danielhokanson/3input-3output-LiFePO4-BatteryBank/sim/output/thermal_year.png

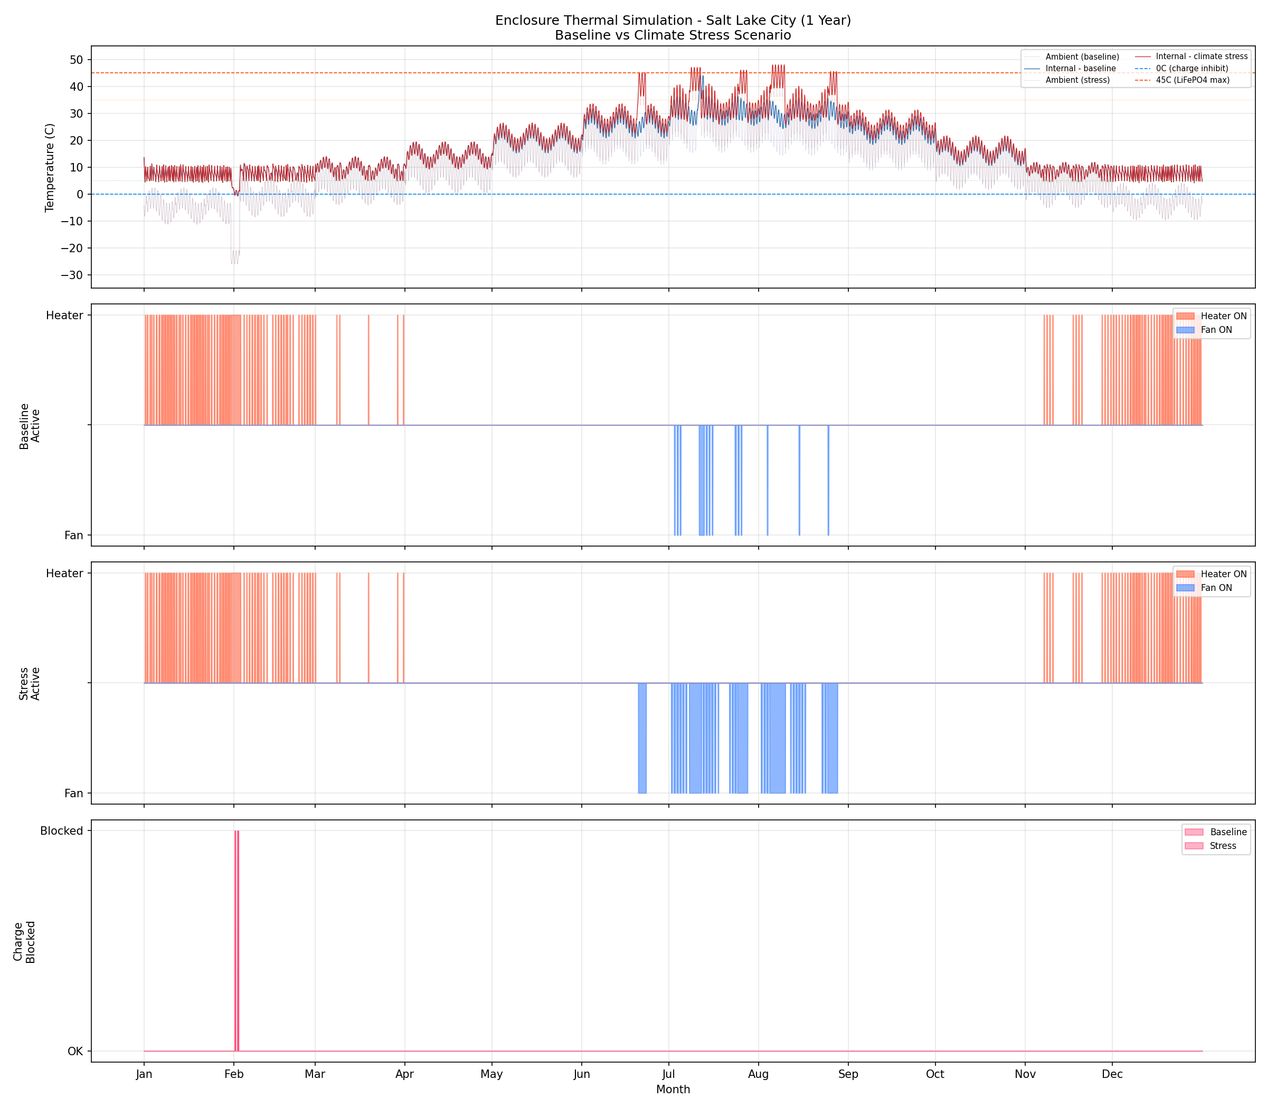
sim/output/thermal_year.png
