danielhokanson/3input-3output-LiFePO4-BatteryBank/cad/main_unit/spacers/4_midwall_spacer_detail.dxf

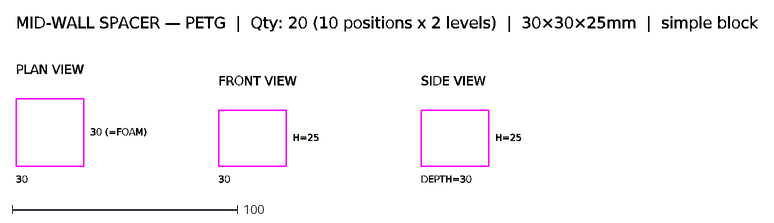
[picture p16: CAD file, 2026-03-13]
cad/main_unit/spacers/4_midwall_spacer_detail.dxf
30
30 (=FOAM)
PLAN VIEW
H=25
FRONT VIEW
DEPTH=30
SIDE VIEW
MID-WALL SPACER — PETG | Qty: 20 (10 positions x 2 levels) | 30×30×25mm | simple block
