danielhokanson/3input-3output-LiFePO4-BatteryBank/cad/satellite_unit/dxf/6_cell_layout_detail.dxf

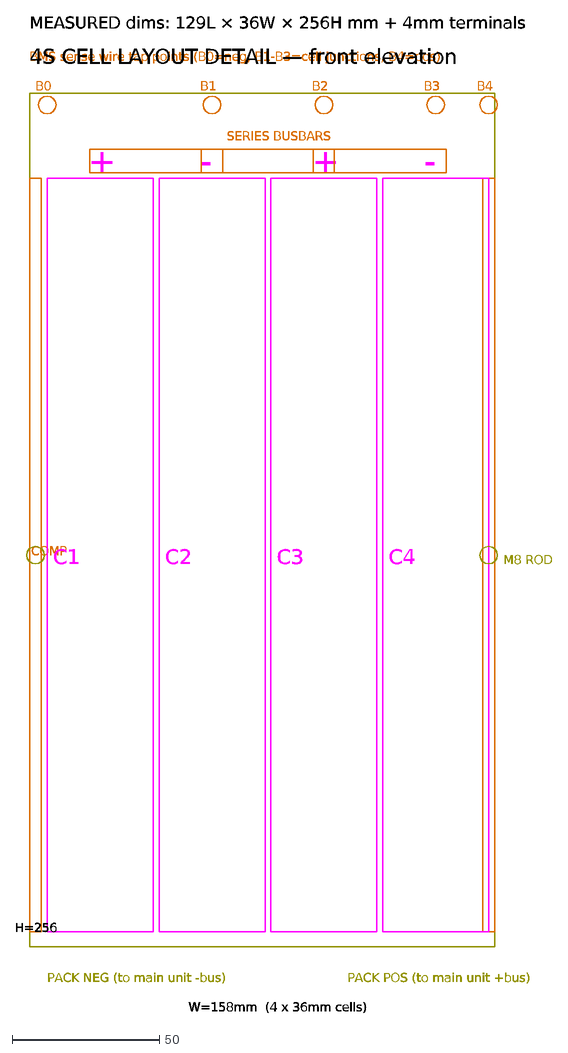
[picture p17: CAD file, 2026-03-13]
cad/satellite_unit/dxf/6_cell_layout_detail.dxf
COMP
+
C1
-
C2
C3
C4
SERIES BUSBARS
B0
B1
B2
B3
B4
BMS sense wire tap points (B0=neg, B1-B3=cell junctions, B4=pos)
PACK NEG (to main unit -bus)
PACK POS (to main unit +bus)
M8 ROD
H=256
W=158mm (4 x 36mm cells)
4S CELL LAYOUT DETAIL — front elevation
MEASURED dims: 129L × 36W × 256H mm + 4mm terminals
