danielhokanson/3input-3output-LiFePO4-BatteryBank/cad/satellite_unit/spacers/2_spacer_cross_section.dxf

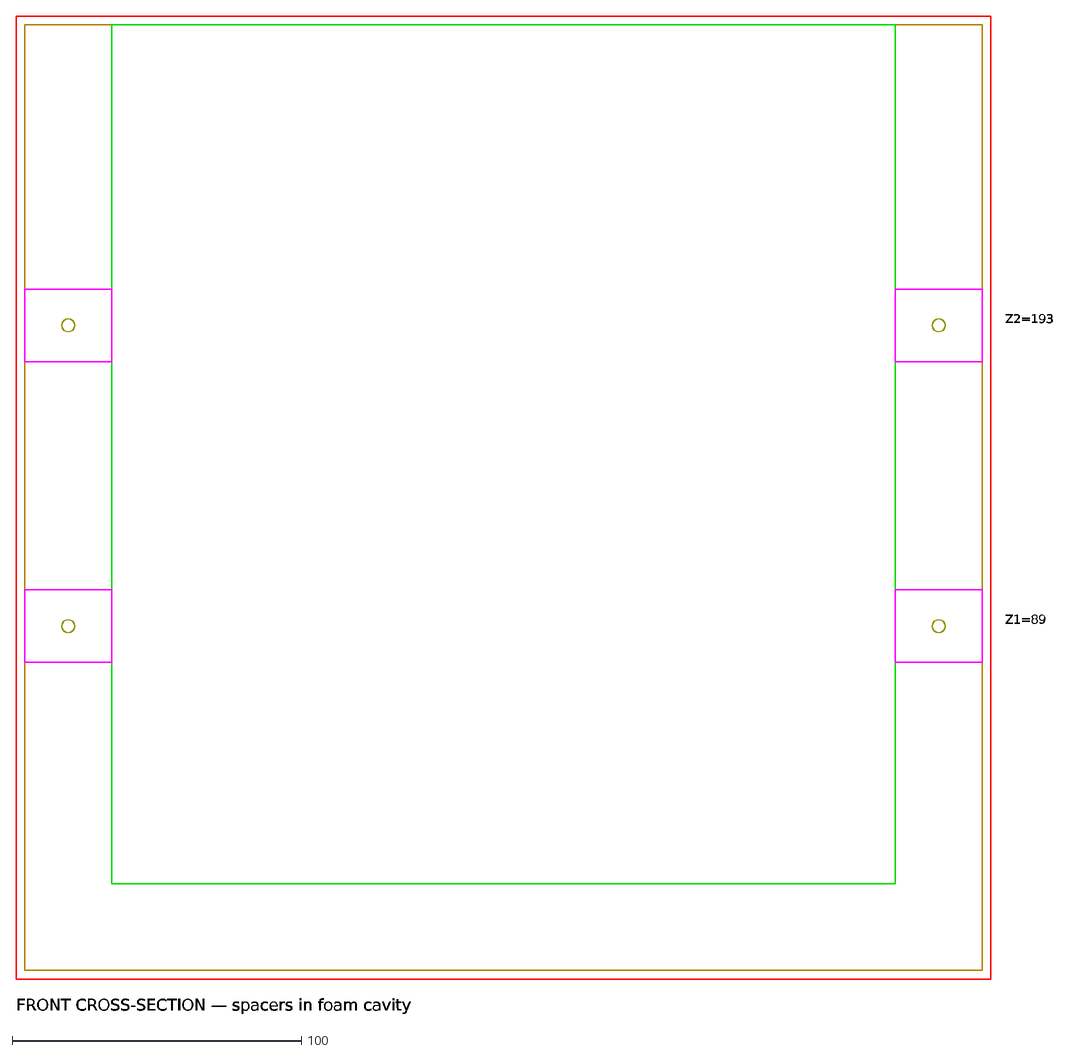
[picture p18: CAD file, 2026-03-13]
cad/satellite_unit/spacers/2_spacer_cross_section.dxf
Z1=89
Z2=193
FRONT CROSS-SECTION — spacers in foam cavity
