danielhokanson/3input-3output-LiFePO4-BatteryBank/cad/main_unit/dxf/4_rear_view.dxf

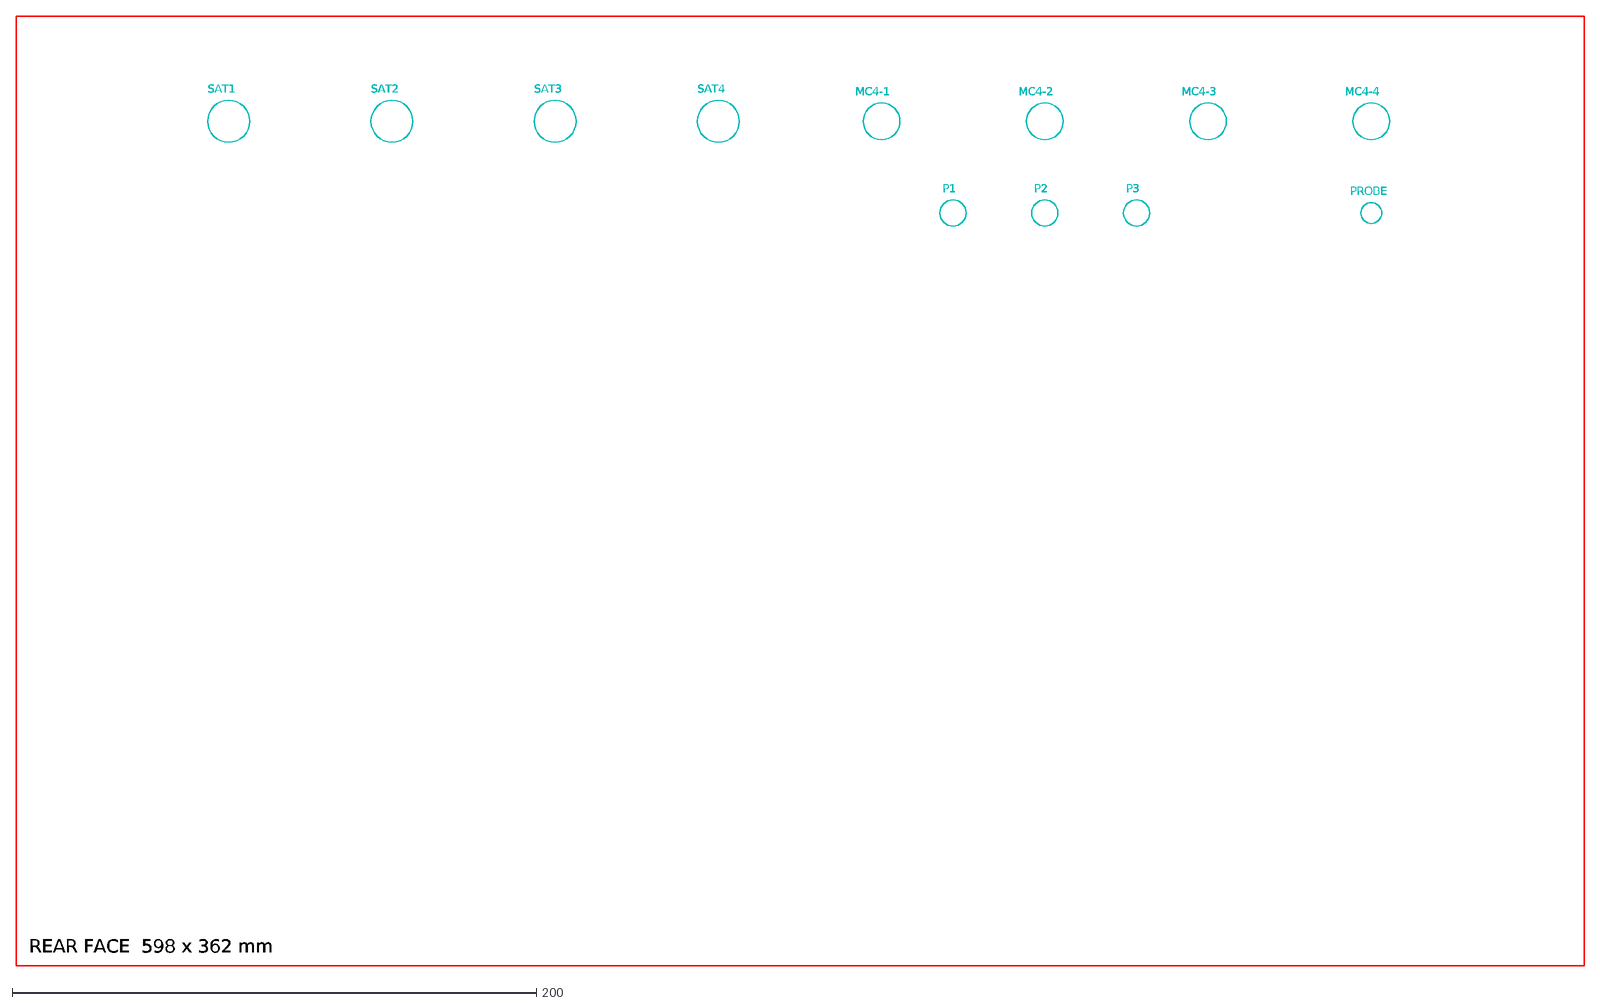
[picture p19: CAD file, 2026-03-13]
cad/main_unit/dxf/4_rear_view.dxf
SAT1
SAT2
SAT3
SAT4
MC4-1
MC4-2
MC4-3
MC4-4
P1
P2
P3
PROBE
REAR FACE 598 x 362 mm
