danielhokanson/3input-3output-LiFePO4-BatteryBank/cad/main_unit/poc stl/Lid (POC 39pct).stl

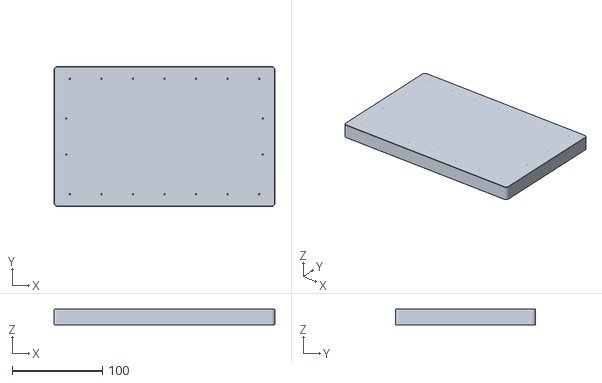
[picture p20: CAD file, 2026-03-13]
cad/main_unit/poc stl/Lid (POC 39pct).stl
245.0 x 155.3 x 17.6
