danielhokanson/3input-3output-LiFePO4-BatteryBank/cad/main_unit/product stl/Shell 1.stl

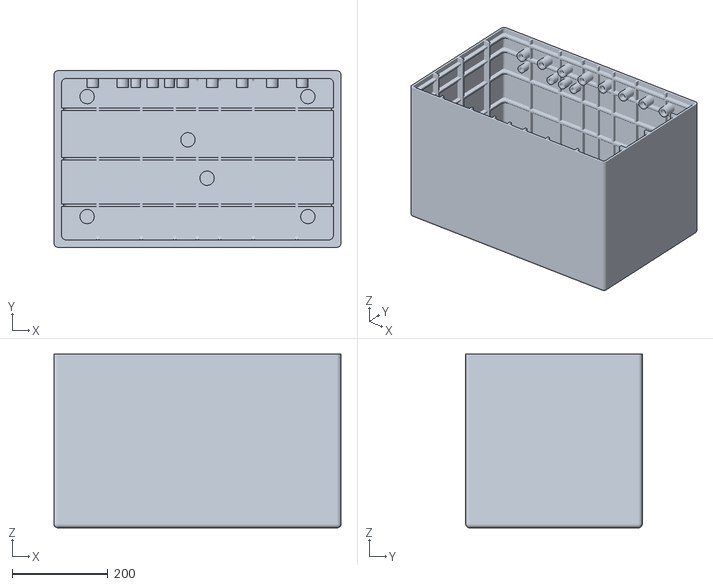
[picture p21: CAD file, 2026-03-13]
cad/main_unit/product stl/Shell 1.stl
598.0 x 368.0 x 362.0
