danielhokanson/3input-3output-LiFePO4-BatteryBank/cad/main_unit/spacers/1_spacer_plan.dxf

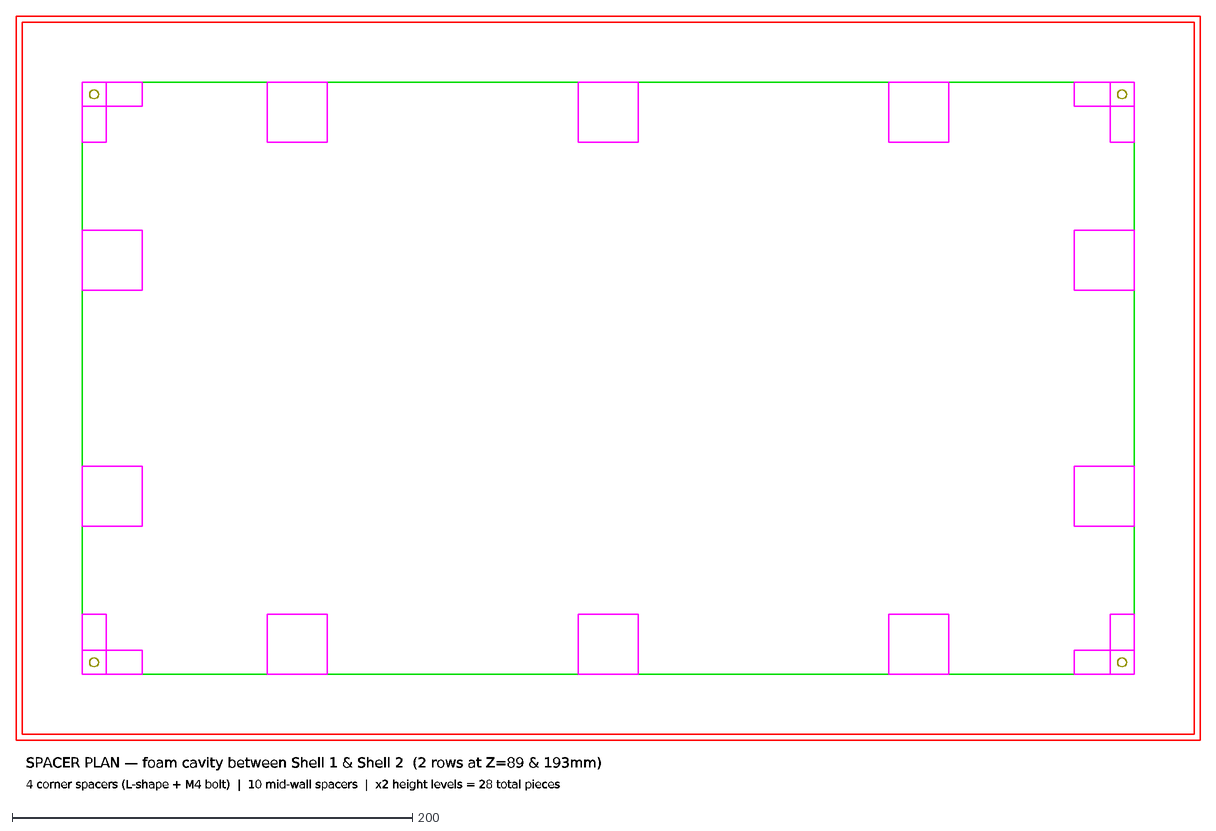
[picture p22: CAD file, 2026-03-13]
cad/main_unit/spacers/1_spacer_plan.dxf
SPACER PLAN — foam cavity between Shell 1 & Shell 2 (2 rows at Z=89 & 193mm)
4 corner spacers (L-shape + M4 bolt) | 10 mid-wall spacers | x2 height levels = 28 total pieces
