danielhokanson/3input-3output-LiFePO4-BatteryBank/cad/satellite_unit/dxf/5_zone_layout.dxf

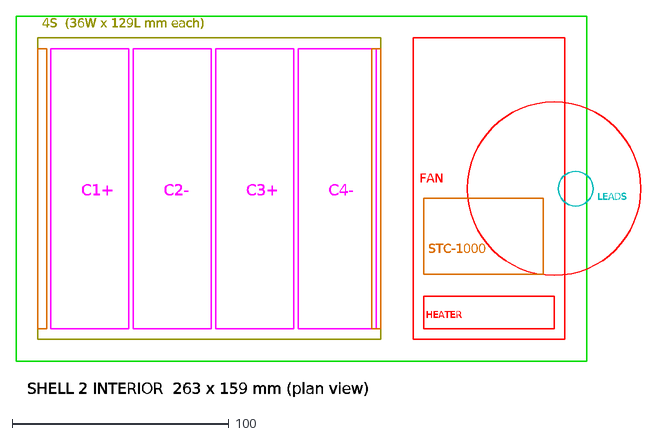
[picture p23: CAD file, 2026-03-13]
cad/satellite_unit/dxf/5_zone_layout.dxf
C1+
C2-
C3+
C4-
4S (36W x 129L mm each)
HEATER
FAN
STC-1000
LEADS
SHELL 2 INTERIOR 263 x 159 mm (plan view)
