danielhokanson/3input-3output-LiFePO4-BatteryBank/cad/satellite_unit/spacers/4_midwall_spacer_detail.dxf

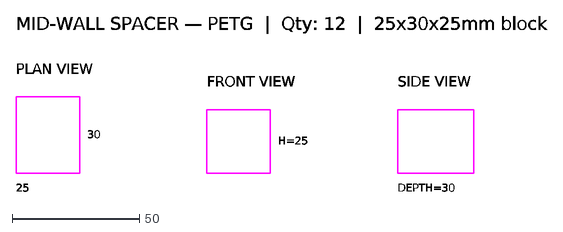
[picture p24: CAD file, 2026-03-13]
cad/satellite_unit/spacers/4_midwall_spacer_detail.dxf
25
30
PLAN VIEW
H=25
FRONT VIEW
DEPTH=30
SIDE VIEW
MID-WALL SPACER — PETG | Qty: 12 | 25x30x25mm block
