danielhokanson/3input-3output-LiFePO4-BatteryBank/cad/main_unit/dxf/9_lid_top_view.dxf

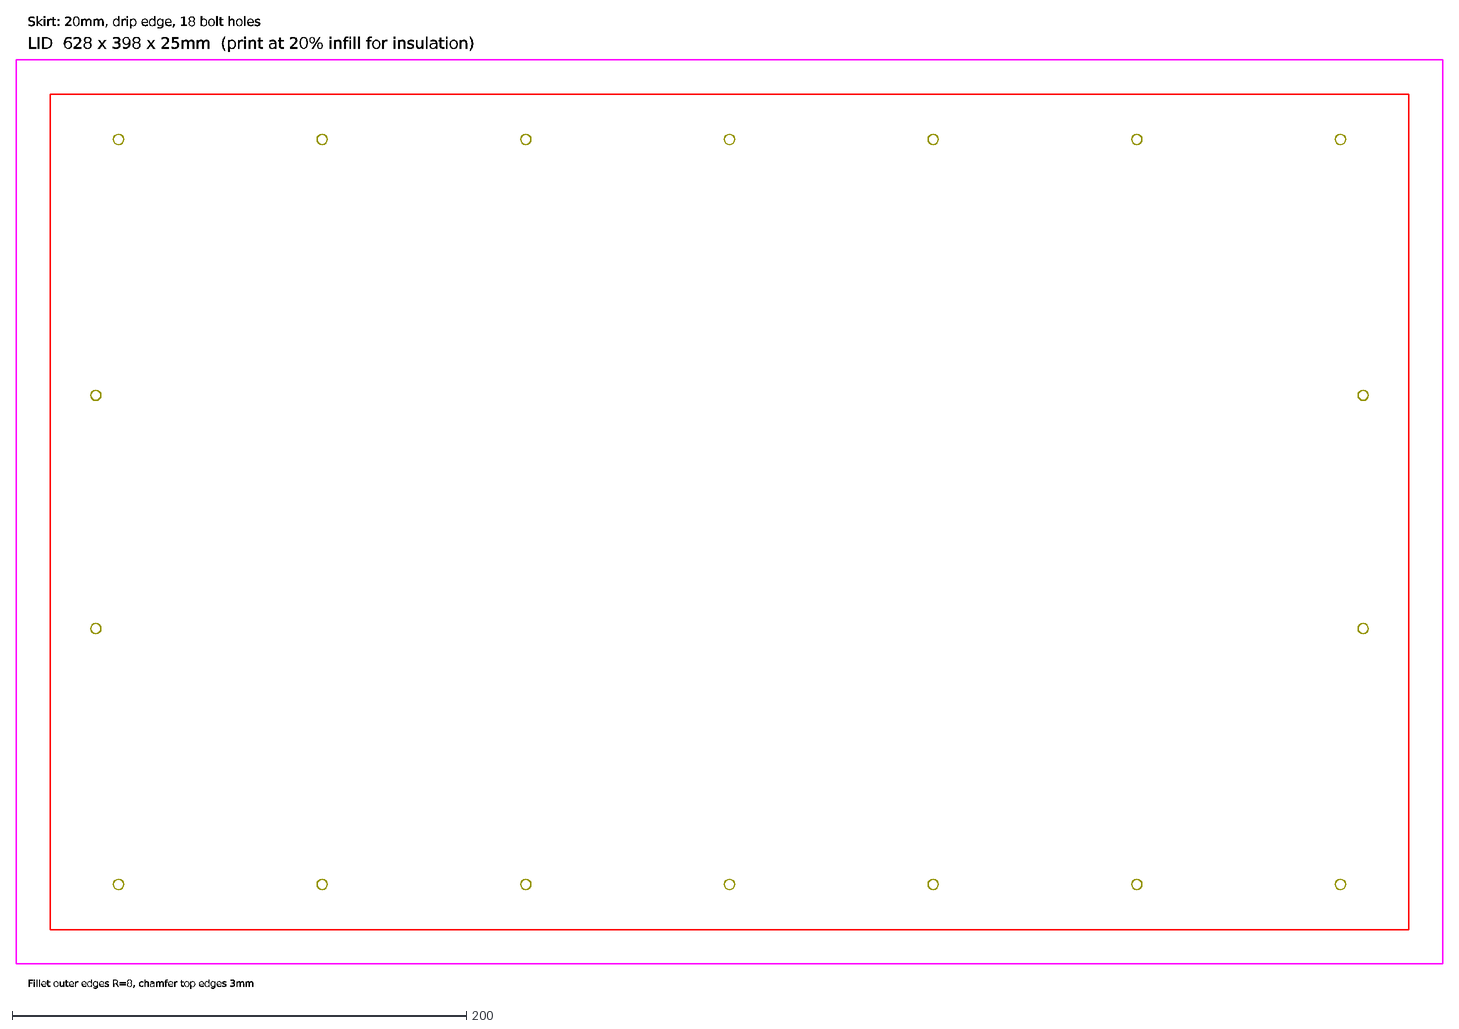
[picture p25: CAD file, 2026-03-13]
cad/main_unit/dxf/9_lid_top_view.dxf
LID 628 x 398 x 25mm (print at 20% infill for insulation)
Skirt: 20mm, drip edge, 18 bolt holes
Fillet outer edges R=8, chamfer top edges 3mm
