danielhokanson/3input-3output-LiFePO4-BatteryBank/cad/satellite_unit/dxf/3_cross_section_side.dxf

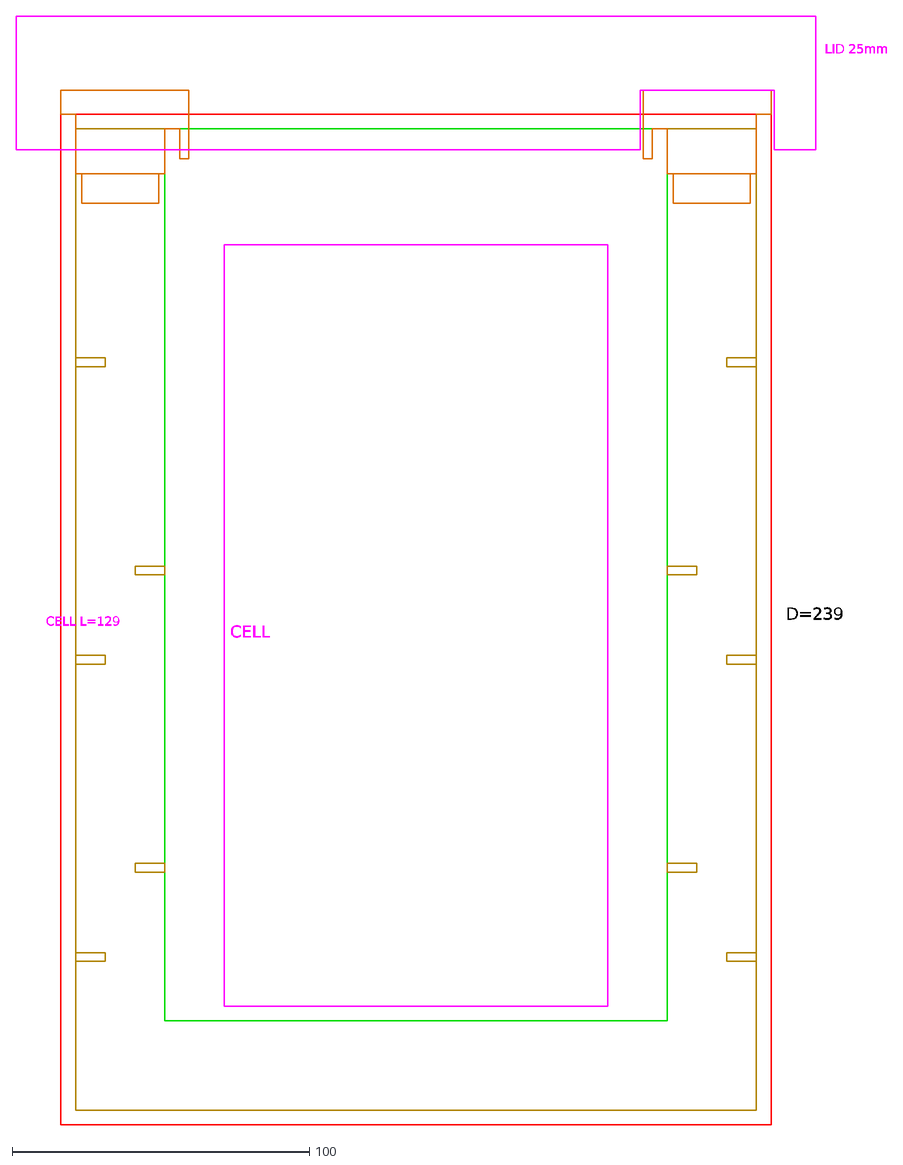
[picture p26: CAD file, 2026-03-13]
cad/satellite_unit/dxf/3_cross_section_side.dxf
CELL
D=239
CELL L=129
LID 25mm
