danielhokanson/3input-3output-LiFePO4-BatteryBank/cad/satellite_unit/dxf/4_lead_exit_view.dxf

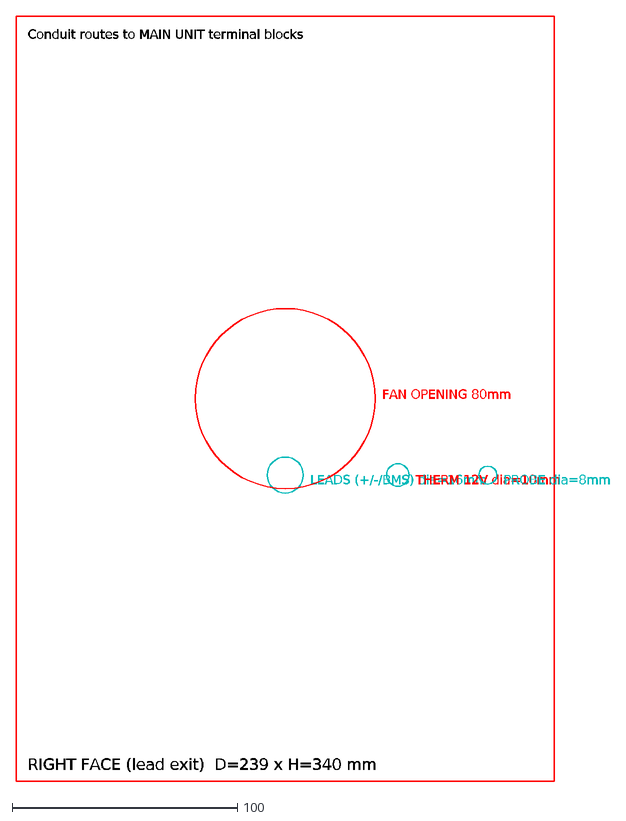
[picture p28: CAD file, 2026-03-13]
cad/satellite_unit/dxf/4_lead_exit_view.dxf
LEADS (+/-/BMS) dia=16mm
THERM 12V dia=10mm
PROBE dia=8mm
FAN OPENING 80mm
RIGHT FACE (lead exit) D=239 x H=340 mm
Conduit routes to MAIN UNIT terminal blocks
