danielhokanson/3input-3output-LiFePO4-BatteryBank/cad/main_unit/dxf/3_cross_section_side.dxf

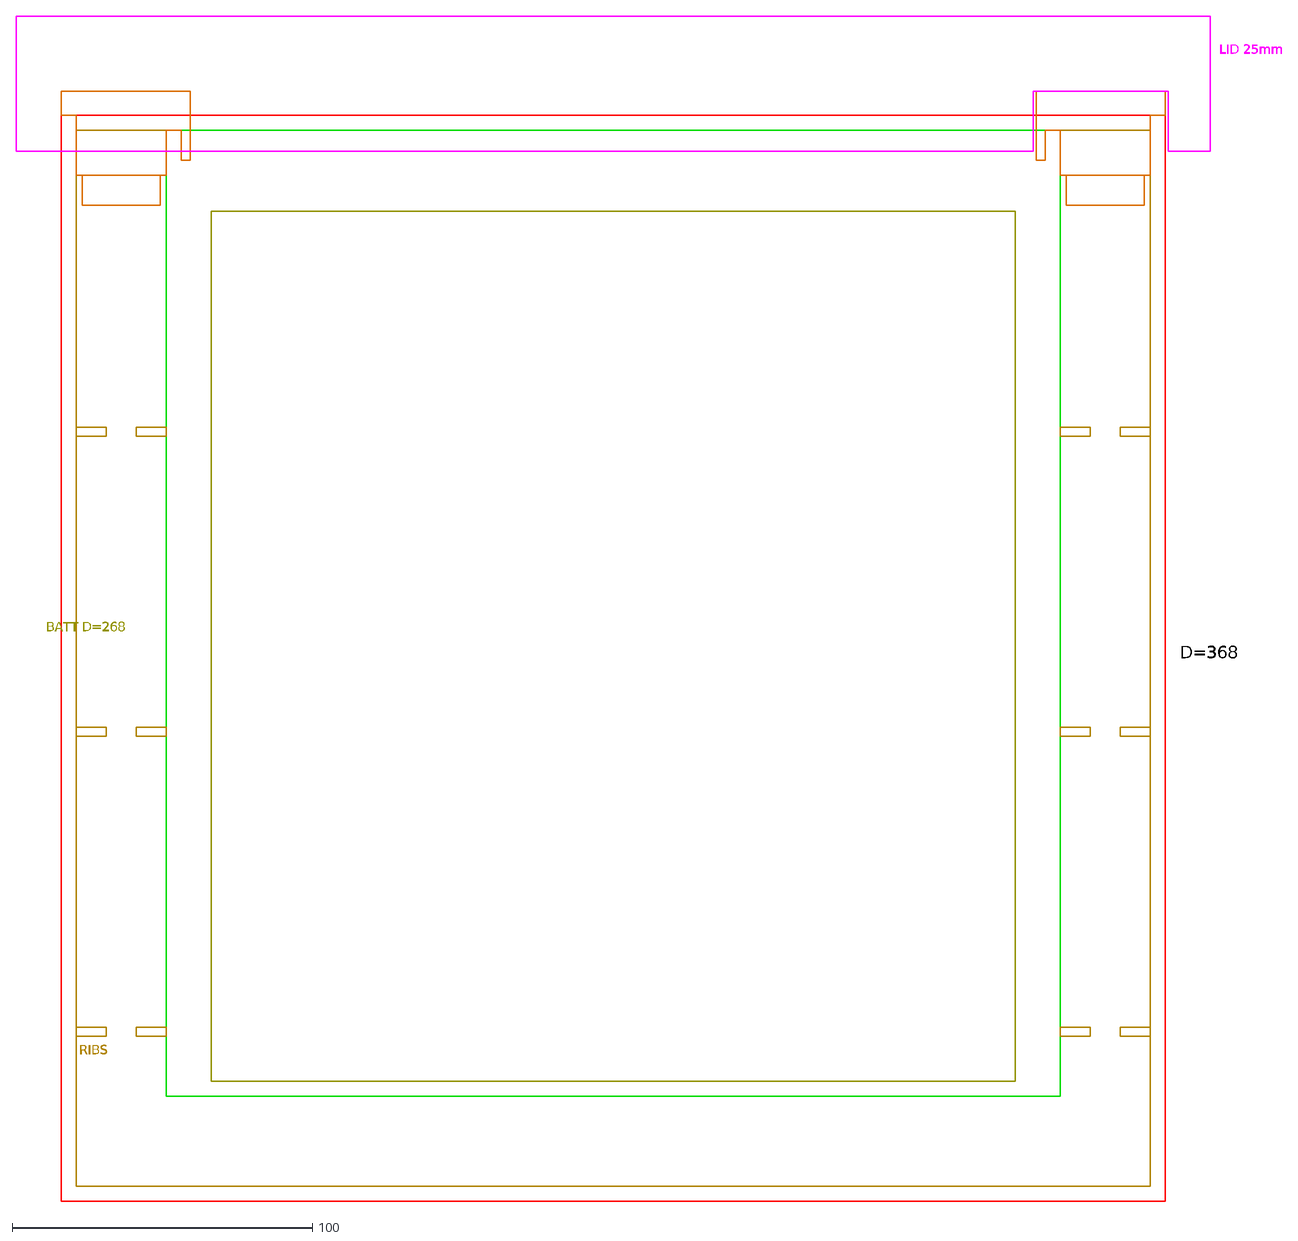
[picture p29: CAD file, 2026-03-13]
cad/main_unit/dxf/3_cross_section_side.dxf
RIBS
LID 25mm
D=368
BATT D=268
