danielhokanson/3input-3output-LiFePO4-BatteryBank/cad/satellite_unit/dxf/1_top_view.dxf

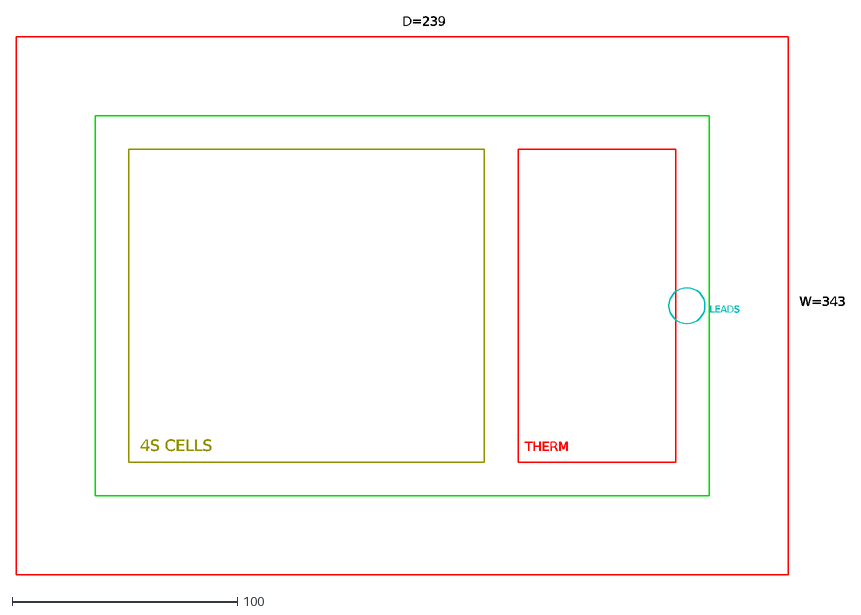
[picture p30: CAD file, 2026-03-13]
cad/satellite_unit/dxf/1_top_view.dxf
4S CELLS
THERM
LEADS
W=343
D=239
