danielhokanson/3input-3output-LiFePO4-BatteryBank/cad/main_unit/dxf/1_top_view.dxf

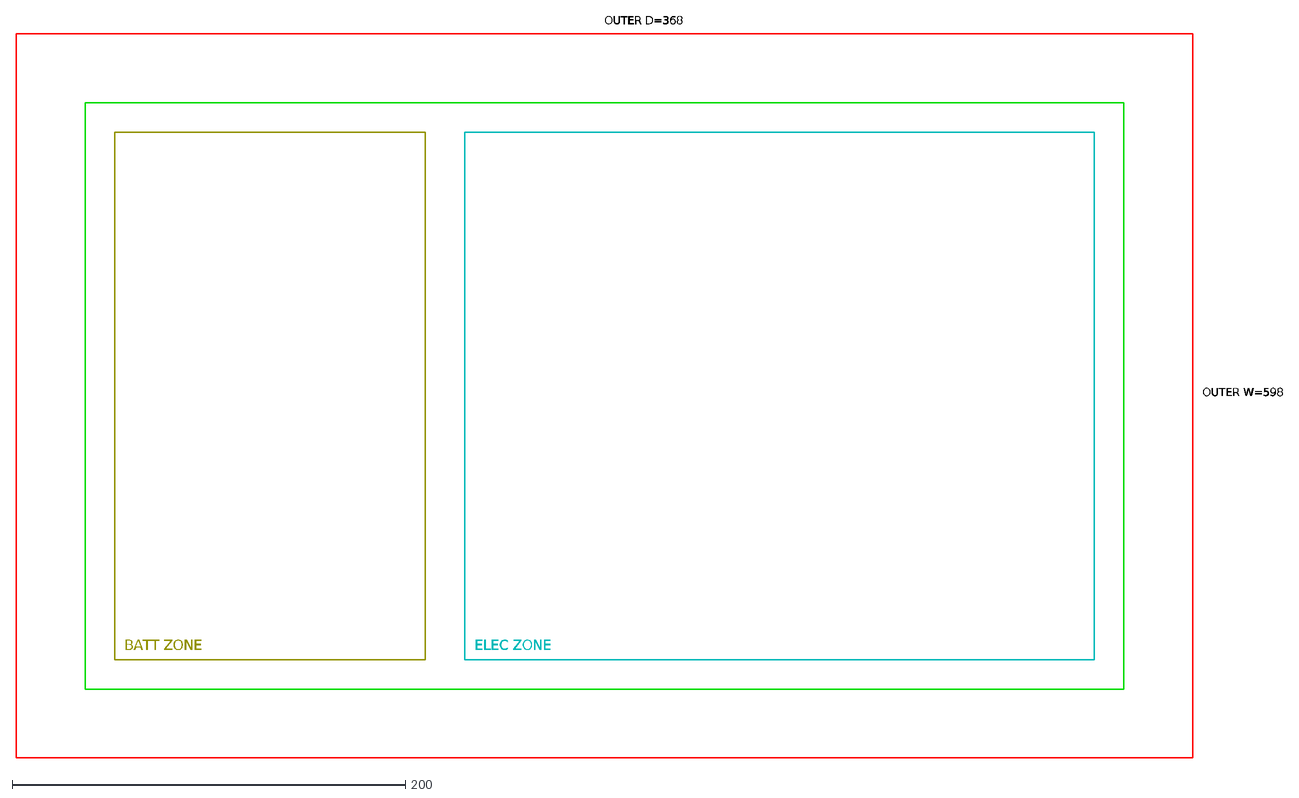
[picture p31: CAD file, 2026-03-13]
cad/main_unit/dxf/1_top_view.dxf
BATT ZONE
ELEC ZONE
OUTER W=598
OUTER D=368
