danielhokanson/3input-3output-LiFePO4-BatteryBank/cad/satellite_unit/dxf/9_lid_top_view.dxf

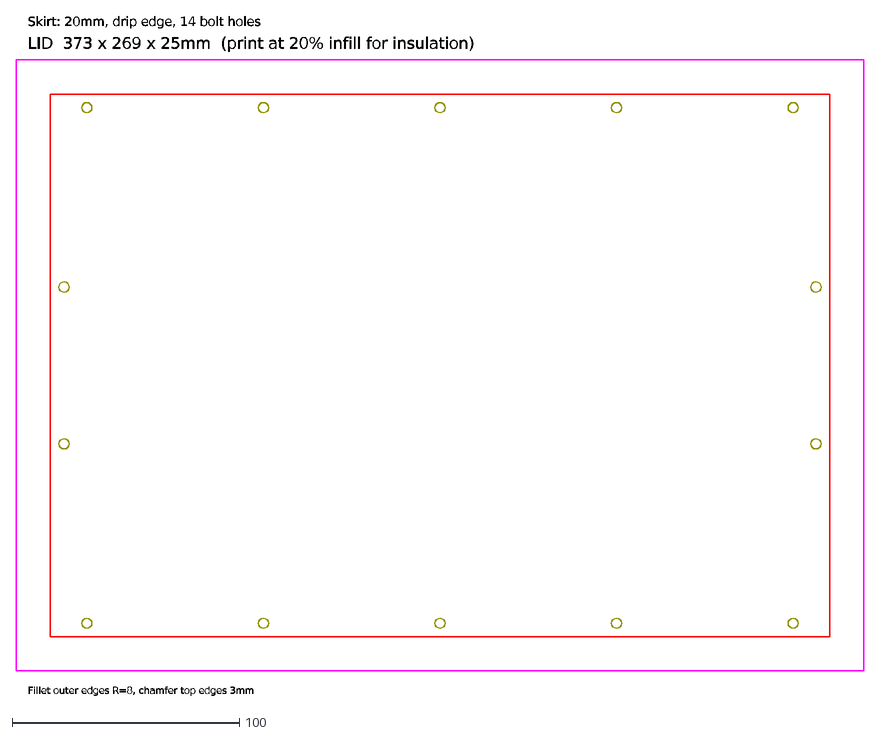
[picture p32: CAD file, 2026-03-13]
cad/satellite_unit/dxf/9_lid_top_view.dxf
LID 373 x 269 x 25mm (print at 20% infill for insulation)
Skirt: 20mm, drip edge, 14 bolt holes
Fillet outer edges R=8, chamfer top edges 3mm
