danielhokanson/3input-3output-LiFePO4-BatteryBank/cad/main_unit/dxf/test_r2010_units.dxf

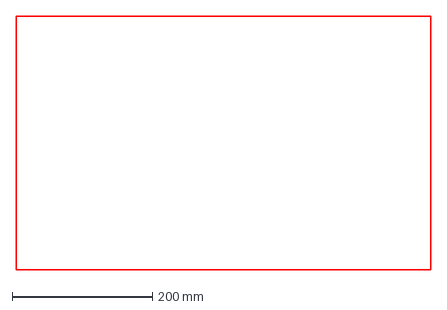
[picture p33: CAD file, 2026-03-13]
cad/main_unit/dxf/test_r2010_units.dxf
592.0 x 362.0 mm
