danielhokanson/3input-3output-LiFePO4-BatteryBank/cad/satellite_unit/dxf/2_cross_section_front.dxf

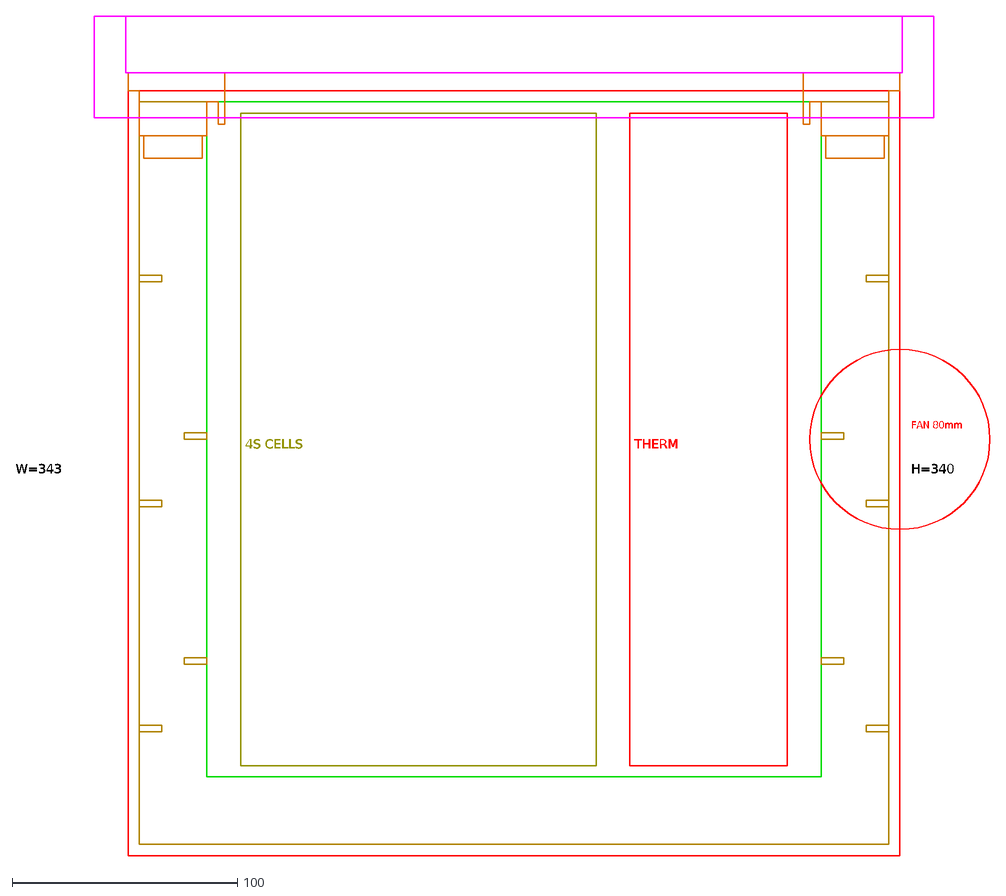
[picture p34: CAD file, 2026-03-13]
cad/satellite_unit/dxf/2_cross_section_front.dxf
4S CELLS
THERM
H=340
W=343
FAN 80mm
