danielhokanson/3input-3output-LiFePO4-BatteryBank/cad/main_unit/dxf/test_r12_lines.dxf

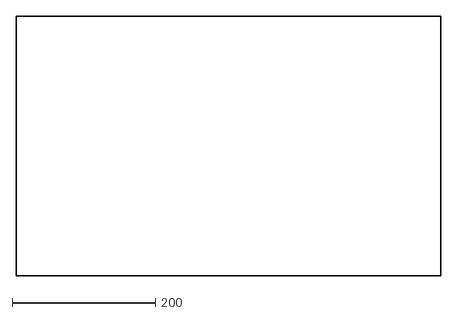
[picture p35: CAD file, 2026-03-13]
cad/main_unit/dxf/test_r12_lines.dxf
592.0 x 362.0
