danielhokanson/3input-3output-LiFePO4-BatteryBank/cad/main_unit/dxf/5_zone_layout.dxf

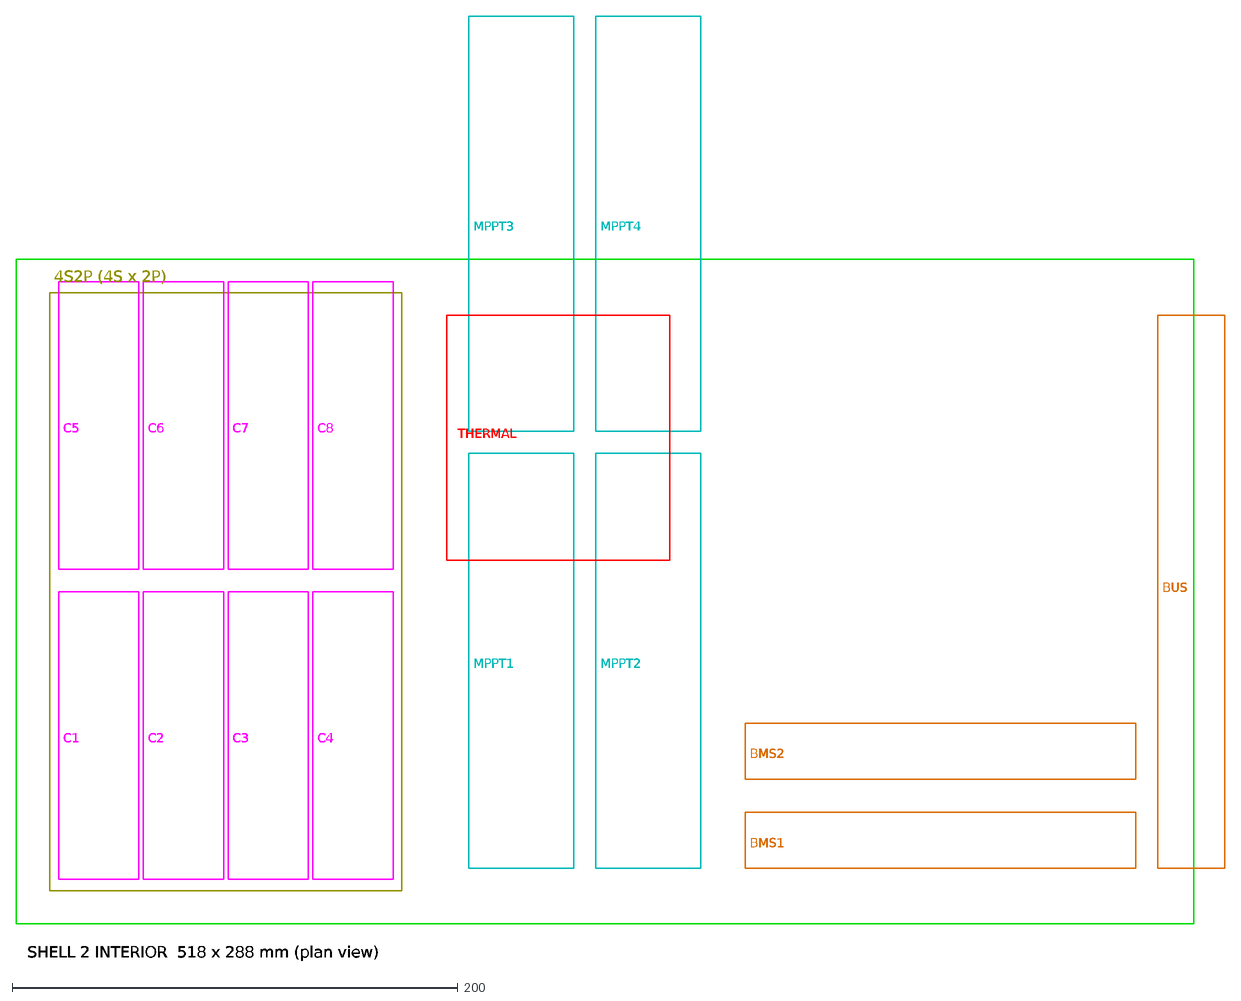
[picture p37: CAD file, 2026-03-13]
cad/main_unit/dxf/5_zone_layout.dxf
C1
C2
C3
C4
C5
C6
C7
C8
4S2P (4S x 2P)
MPPT1
MPPT2
MPPT3
MPPT4
BMS1
BMS2
BUS
THERMAL
SHELL 2 INTERIOR 518 x 288 mm (plan view)
