danielhokanson/3input-3output-LiFePO4-BatteryBank/cad/main_unit/dxf/2_cross_section_front.dxf

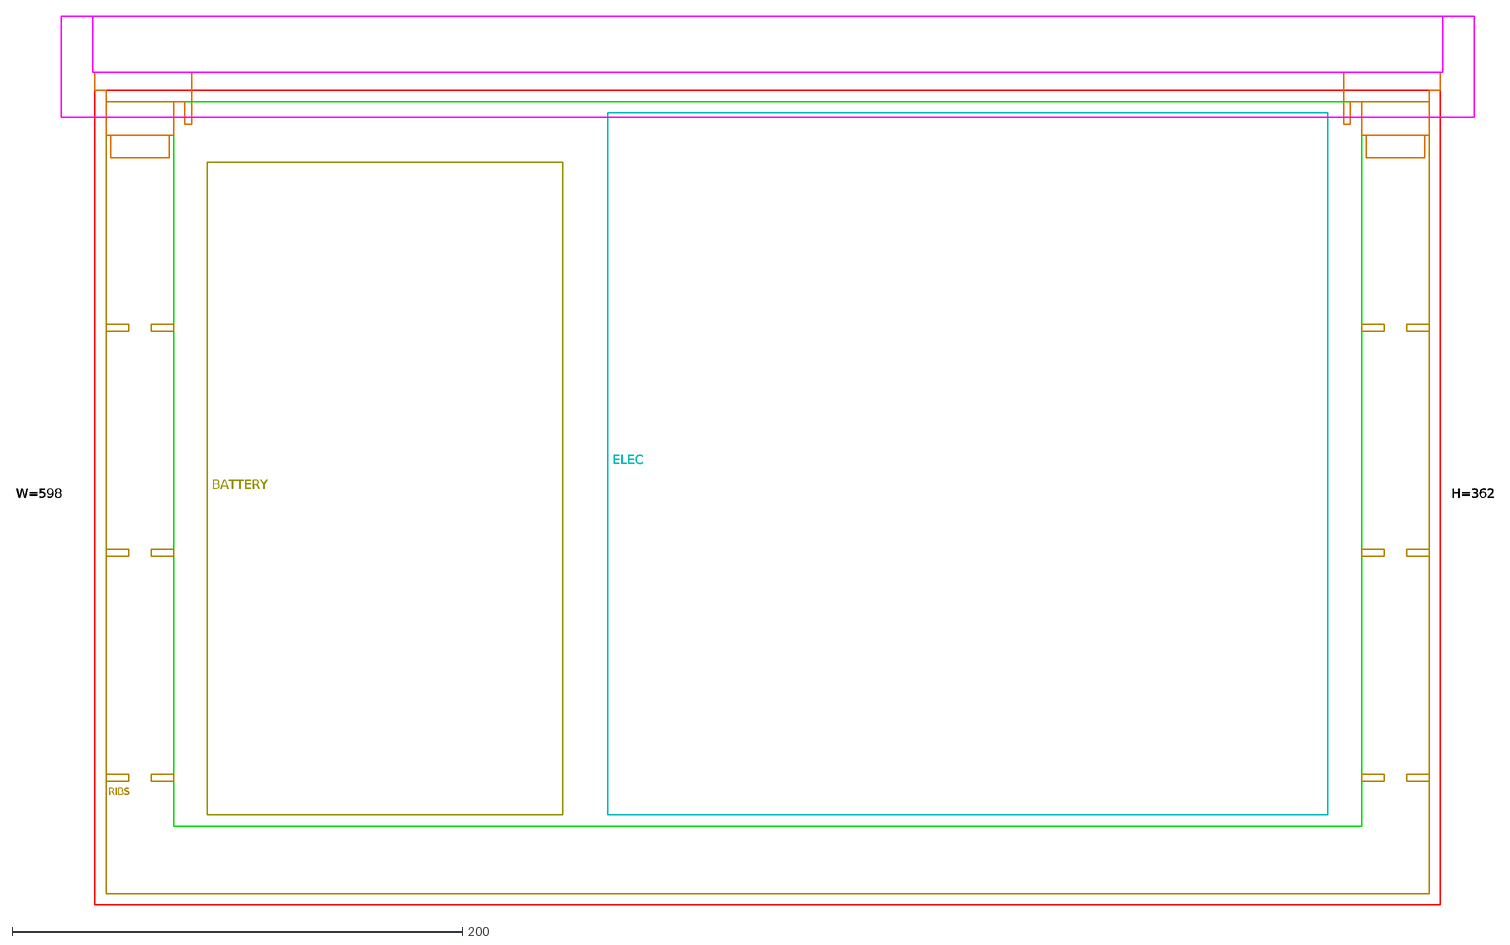
[picture p38: CAD file, 2026-03-13]
cad/main_unit/dxf/2_cross_section_front.dxf
BATTERY
ELEC
RIBS
H=362
W=598
