danielhokanson/3input-3output-LiFePO4-BatteryBank/cad/main_unit/dxf/7_cap_top_view.dxf

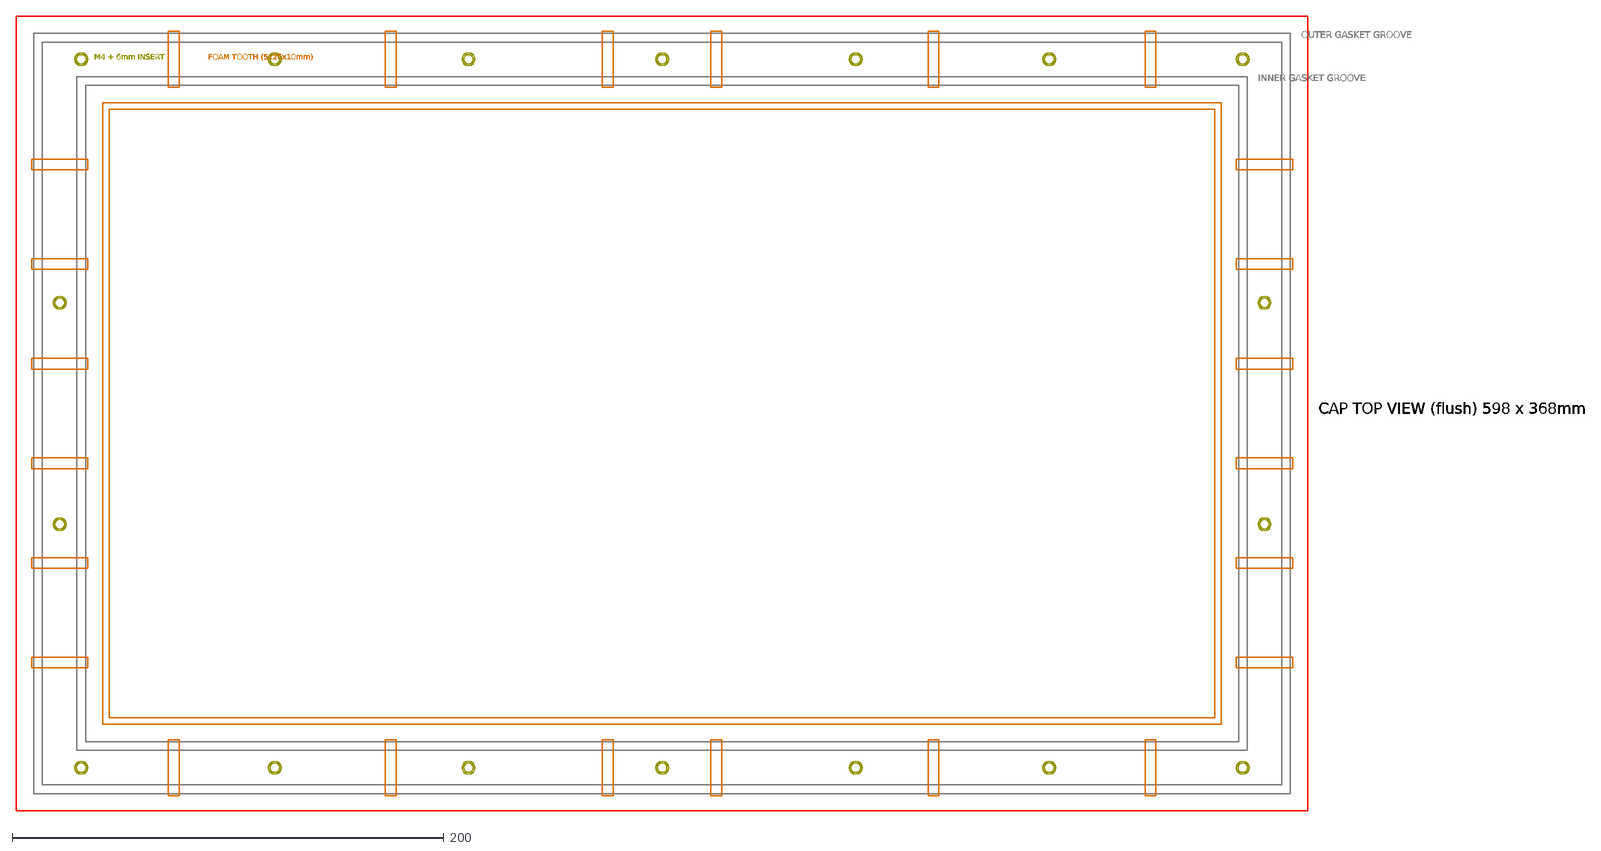
[picture p39: CAD file, 2026-03-13]
cad/main_unit/dxf/7_cap_top_view.dxf
CAP TOP VIEW (flush) 598 x 368mm
OUTER GASKET GROOVE
INNER GASKET GROOVE
M4 + 6mm INSERT
FOAM TOOTH (5x26x10mm)
